Cyrille-de-Brebisson/eq_control/Firmware/eqControl_Ino/catalogs.h

// This code is copyright Cyrille de Brebisson
// Contact me if you want to use all or part of it.
// Most likely I will say yes unless it is for commercial use at which point we can discuss

void getRaDecPos(uint8_t const *s, int32_t &ra, int32_t &dec) // extract ra/dec from 3 program memory bytes that containthe data with 12 bit precision
{
    uint8_t b1= pgm_read_byte(s), b2= pgm_read_byte(s+1), b3= pgm_read_byte(s+2);
    ra= (b1+(uint32_t(b2&0xf)<<8))*(24*3600L)/4096;
    dec= ((b2>>4)+(uint32_t(b3)<<4))*(180*3600L)/4096-90*3600L;
}

// NCG Objects with Mag up to 11,  738 items: 2.9Kb bytes
// iDiff is the difference in index from NgcDiff[i+1] to NgcDiff[i]. Saves 700 bytes compared with using a 16 bit number...
// so first object is ngc40, followed by ngc45 and 55
struct { uint8_t idDiff; uint8_t radec[3]; } const NgcDiff[] PROGMEM ={
    { 40, {37, 32, 231}},
    { 5, {40, 0, 95}},
    { 10, {42, 64, 72}},
    { 48, {72, 64, 215}},
    { 1, {68, 112, 25}},
    { 17, {76, 64, 26}},
    { 8, {84, 160, 213}},
    { 4, {88, 16, 218}},
    { 1, {86, 176, 80}},
    { 12, {94, 0, 218}},
    { 1, {94, 240, 196}},
    { 10, {98, 0, 116}},
    { 28, {111, 176, 196}},
    { 3, {125, 80, 249}},
    { 1, {112, 208, 214}},
    { 16, {114, 64, 187}},
    { 5, {115, 64, 108}},
    { 11, {121, 16, 186}},
    { 3, {121, 176, 186}},
    { 1, {123, 208, 215}},
    { 21, {133, 16, 111}},
    { 1, {133, 112, 98}},
    { 6, {135, 0, 92}},
    { 25, {148, 160, 195}},
    { 3, {150, 128, 208}},
    { 7, {150, 48, 90}},
    { 12, {156, 96, 74}},
    { 30, {160, 224, 24}},
    { 16, {168, 80, 25}},
    { 16, {179, 48, 27}},
    { 19, {194, 144, 215}},
    { 23, {197, 192, 178}},
    { 15, {194, 80, 24}},
    { 17, {215, 160, 211}},
    { 21, {224, 240, 210}},
    { 31, {232, 112, 135}},
    { 36, {241, 128, 141}},
    { 35, {254, 0, 218}},
    { 19, {1, 193, 95}},
    { 3, {9, 81, 214}},
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
};

static int const nbNgc= sizeof(NgcDiff)/sizeof(NgcDiff[0])-12; // the last 12 objects are not NGC, but messiers or cadwell that are not ngcs...

class CNgc { public: // A class for scanning through ngs... works incrementally due to the idiff...
    uint16_t internalId= 0; // indicate internal id (0 to nbNgc-1)
    uint16_t externalId= 40; // indicate NGC number of current NGC
    void next() { if (internalId>=nbNgc-1) return; internalId++; externalId+= pgm_read_byte(&(NgcDiff[internalId].idDiff)); }
    void prev() { if (internalId==0) return; externalId-= pgm_read_byte(&(NgcDiff[internalId].idDiff)); internalId--; }
    void pos(int32_t &ra, int32_t &dec) { getRaDecPos(NgcDiff[internalId].radec, ra, dec); }
} Ngc;

// Messiers and Cadwell are pointers to ngc numbers. These are 10 bit packed to save around 300 bytes
static uint8_t const MessierToNgc10[] PROGMEM = {152, 64, 27, 31, 136, 17, 106, 41, 230, 154, 73, 238, 72, 169, 140, 46, 102, 217, 236, 159, 129, 2, 250, 227, 153, 110, 54, 58, 38, 159, 248, 74, 250, 42, 161, 184, 74, 43, 65, 4, 42, 16, 113, 139, 38, 172, 80, 18, 109, 190, 208, 132, 66, 202, 67, 94, 200, 243, 206, 65, 168, 89, 179, 158, 187, 225, 93, 90, 106, 168, 153, 242, 38, 156, 113, 144, 245, 72, 222, 117, 96, 137, 117, 81, 111, 134, 62, 234, 170, 175, 192, 178, 0, 171, 11, 72, 168, 34, 137, 135, 43, 181, 212, 30, 102, 153, 113, 182, 154, 107, 182, 233, 86, 155, 146, 245, 68, 135, 148, 82, 90, 13, 166, 152, 100, 249, 229, 119, 130, 111, 77, 45, 134, 162, 85, 116, 61, 0, };
uint16_t const nbMessier= 110;
static uint8_t const CadwellToNgc10[] PROGMEM = {13, 0, 128, 88, 177, 250, 202, 169, 78, 9, 251, 202, 192, 46, 175, 34, 232, 176, 42, 183, 10, 48, 192, 175, 176, 163, 189, 203, 195, 19, 236, 36, 102, 171, 13, 223, 137, 219, 239, 112, 191, 246, 186, 221, 109, 181, 226, 118, 78, 88, 254, 14, 123, 175, 185, 239, 41, 147, 171, 70, 195, 20, 243, 111, 115, 51, 253, 67, 44, 5, 169, 130, 243, 211, 93, 120, 85, 240, 109, 56, 22, 20, 168, 196, 166, 68, 106, 160, 143, 0, 140, 208, 20, 98, 141, 230, 197, 201, 19, 122, 76, 174, 200, 221, 124, 0, 91, 233, 196, 130, 29, 134, 84, 213, 82, 158, 82, 167, 97, 64, 106, 1, 23, 176, 192, 157, 14, 188, 74, 7, 216, 17, 240, 225, 101, 58, 1, };
uint16_t const nbCadwell= 109;
static uint16_t read10bits(uint8_t const *p, uint8_t v) // read the nth 10 bit number from lists above...
{
    uint16_t t= pgm_read_word(p+((v*10)>>3)); 
    t= (t>>((v&3)*2))&1023;
    return t;
}

// named star catalog. 1507 bytes, (133 stars)
// form is 3 bytes ra/dec on a 0-4095 range 
// then 1 byte: star name size -3 (low order nibble) and previous's start name size-3 (high order nibble) (for backward scann)
// and finally the star name
// Note that should we move the star name to 5 bit per character, we could save around 300 bytes!
class CStars { public:
    // This class handles the star list, giving you a pointer on a star and allowing you to go througth it as you want and get the info...
    uint8_t const *s= stars;      // pointer to current selected star
    static const int nb= 133;     // total number of stars
    uint8_t id= 0;                // id of current star (to avoid going past ends)
    static uint8_t const stars[]; // star table...
    void next() { if (id>=nb-1) return; id++; s= s+4+(pgm_read_byte(s+3)&15)+3; }
    void prev() { if (id==0) return; id--; s= s-4-(((pgm_read_byte(s+3)>>4)&15)+3); }
    void pos(int32_t &ra, int32_t &dec) { getRaDecPos(s, ra, dec); }
    int8_t name(char *n) { int8_t l= (pgm_read_byte(s+3)&15)+3; int8_t l2= l; n[l]= 0; while (--l>=0) n[l]=pgm_read_byte(s+4+l); return l2; } // copy current star name in n. return it's size. max=18
} stars;
uint8_t const CStars::stars[] PROGMEM ={
    251, 161, 70,  0x03,'A','c','a','m','a','r', //Acamar
    21, 145, 46,  0x35,'A','c','h','e','r','n','a','r', //Achernar
    75, 72, 38,  0x52,'A','c','r','u','x', //Acrux
    166, 196, 86,  0x23,'A','d','h','a','r','a', //Adhara
    198, 28, 98,  0x35,'A','l','b','a','l','d','a','h', //Albaldah
    2, 205, 167,  0x54,'A','l','b','i','r','e','o', //Albireo
    242, 56, 206,  0x42,'A','l','c','o','r', //Alcor
    135, 66, 162,  0x24,'A','l','c','y','o','n','e', //Alcyone
    16, 115, 151,  0x46,'A','l','d','e','b','a','r','a','n', //Aldebaran
    52, 14, 217,  0x66,'A','l','d','e','r','a','m','i','n', //Alderamin
    37, 144, 149,  0x64,'A','l','g','e','n','i','b', //Algenib
    227, 54, 156,  0x44,'A','l','g','i','e','b','a', //Algieba
    23, 50, 186,  0x42,'A','l','g','o','l', //Algol
    84, 136, 104,  0x24,'A','l','g','o','r','a','b', //Algorab
    107, 84, 151,  0x43,'A','l','h','e','n','a', //Alhena
    153, 152, 207,  0x33,'A','l','i','o','t','h', //Alioth
    49, 41, 198,  0x33,'A','l','k','a','i','d', //Alkaid
    96, 49, 188,  0x33,'A','l','m','a','a','k', //Almaak
    194, 62, 61,  0x33,'A','l','n','a','i','r', //Alnair
    160, 163, 168,  0x33,'A','l','n','a','t','h', //Alnath
    188, 67, 126,  0x34,'A','l','n','i','l','a','m', //Alnilam
    201, 51, 125,  0x44,'A','l','n','i','t','a','k', //Alnitak
    78, 166, 115,  0x44,'A','l','p','h','a','r','d', //Alphard
    98, 250, 165,  0x45,'A','l','p','h','e','k','k','a', //Alphekka
    23, 80, 169,  0x56,'A','l','p','h','e','r','a','t','z', //Alpheratz
    71, 29, 137,  0x64,'A','l','s','h','a','i','n', //Alshain
    59, 157, 140,  0x43,'A','l','t','a','i','r', //Altair
    239, 84, 86,  0x33,'A','l','u','d','r','a', //Aludra
    74, 208, 67,  0x32,'A','n','k','a','a', //Ankaa
    254, 106, 90,  0x24,'A','n','t','a','r','e','s', //Antares
    129, 73, 155,  0x45,'A','r','c','t','u','r','u','s', //Arcturus
    178, 163, 102,  0x52,'A','r','n','e','b', //Arneb
    53, 219, 29,  0x22,'A','t','r','i','a', //Atria
    149, 85, 43,  0x22,'A','v','i','o','r', //Avior
    40, 15, 207,  0x2b,'B','a','b','c','o','c','k','\'','s',' ','s','t','a','r', //Babcock's star
    249, 171, 134,  0xbb,'B','a','r','n','a','r','d','\'','s',' ','S','t','a','r', //Barnard's Star
    135, 24, 43,  0xb3,'B','e','c','r','u','x', //Becrux
    156, 3, 137,  0x36,'B','e','l','l','a','t','r','i','x', //Bellatrix
    242, 131, 138,  0x67,'B','e','t','e','l','g','e','u','s','e', //Betelgeuse
    68, 4, 53,  0x74,'C','a','n','o','p','u','s', //Canopus
    132, 99, 193,  0x44,'C','a','p','e','l','l','a', //Capella
    26, 16, 212,  0x41,'C','a','p','h', //Caph
    13, 85, 173,  0x13,'C','a','s','t','o','r', //Castor
    208, 123, 134,  0x35,'C','e','b','a','l','r','a','i', //Cebalrai
    161, 80, 214,  0x50,'C','i','h', //Cih
    159, 120, 182,  0x07,'C','o','r',' ','C','a','r','o','l','i', //Cor Caroli
    107, 195, 120,  0x72,'C','u','r','s','a', //Cursa
    80, 29, 178,  0x27,'C','y','g','n','u','s',' ','X','-','1', //Cygnus X-1
    203, 109, 192,  0x72,'D','e','n','e','b', //Deneb
    224, 183, 148,  0x25,'D','e','n','e','b','o','l','a', //Denebola
    123, 96, 102,  0x53,'D','i','p','h','d','a', //Diphda
    171, 218, 95,  0x35,'D','s','c','h','u','b','b','a', //Dschubba
    95, 215, 215,  0x52,'D','u','b','h','e', //Dubhe
    125, 14, 142,  0x21,'E','n','i','f', //Enif
    246, 59, 201,  0x13,'E','t','a','m','i','n', //Etamin
    78, 223, 85,  0x36,'F','o','m','a','l','h','a','u','t', //Fomalhaut
    88, 200, 46,  0x63,'G','a','c','r','u','x', //Gacrux
    216, 93, 176,  0x33,'G','i','e','n','a','h', //Gienah
    44, 8, 103,  0x3a,'G','i','e','n','a','h',' ','G','h','u','r','a','b', //Gienah Ghurab
    247, 196, 139,  0xa4,'G','o','m','e','i','s','a', //Gomeisa
    186, 218, 99,  0x45,'G','r','a','f','f','i','a','s', //Graffias
    235, 167, 181,  0x5d,'G','r','o','o','m','b','r','i','d','g','e',' ','1','8','3','0', //Groombridge 1830
    96, 41, 42,  0xd2,'H','a','d','a','r', //Hadar
    105, 81, 161,  0x22,'H','a','m','a','l', //Hamal
    76, 35, 175,  0x25,'H','a','s','s','a','l','e','h', //Hassaleh
    186, 147, 119,  0x53,'H','a','t','s','y','a', //Hatsya
    213, 137, 166,  0x31,'I','z','a','r', //Izar
    118, 243, 63,  0x1b,'K','a','p','t','e','y','n','\'','s',' ','S','t','a','r', //Kapteyn's Star
    68, 28, 79,  0xbb,'K','a','u','s',' ','A','u','s','t','r','a','l','i','s', //Kaus Australis
    79, 220, 91,  0xba,'K','a','u','s',' ','B','o','r','e','a','l','i','s', //Kaus Borealis
    59, 156, 85,  0xae,'K','a','u','s',' ','M','e','r','i','d','i','o','n','a','l','i','s', //Kaus Meridionalis
    229, 121, 233,  0xe3,'K','o','c','h','a','b', //Kochab
    0, 155, 158,  0x38,'K','o','r','n','e','p','h','o','r','o','s', //Kornephoros
    97, 184, 94,  0x81,'K','r','a','z', //Kraz
    98, 159, 149,  0x13,'M','a','r','k','a','b', //Markab
    36, 255, 170,  0x32,'M','a','t','a','r', //Matar
    43, 24, 209,  0x23,'M','e','g','r','e','z', //Megrez
    254, 227, 191,  0x37,'M','e','n','k','a','l','i','n','a','n', //Menkalinan
    6, 210, 133,  0x73,'M','e','n','k','a','r', //Menkar
    104, 73, 76,  0x34,'M','e','n','k','e','n','t', //Menkent
    90, 55, 208,  0x42,'M','e','r','a','k', //Merak
    37, 214, 28,  0x28,'M','i','a','p','l','a','c','i','d','u','s', //Miaplacidus
    176, 147, 127,  0x84,'M','i','n','t','a','k','a', //Mintaka
    140, 193, 123,  0x41,'M','i','r','a', //Mira
    198, 160, 178,  0x13,'M','i','r','a','c','h', //Mirach
    69, 226, 198,  0x34,'M','i','r','p','h','a','k', //Mirphak
    64, 116, 102,  0x43,'M','i','r','z','a','m', //Mirzam
    238, 24, 206,  0x32,'M','i','z','a','r', //Mizar
    70, 41, 154,  0x23,'M','u','f','r','i','d', //Mufrid
    95, 21, 71,  0x31,'N','a','o','s', //Naos
    16, 188, 84,  0x11,'N','a','s','h', //Nash
    165, 115, 98,  0x12,'N','i','h','a','l', //Nihal
    157, 156, 90,  0x22,'N','u','n','k','i', //Nunki
    27, 17, 48,  0x26,'p',' ','E','r','i','d','a','n','i', //p Eridani
    158, 77, 47,  0x64,'P','e','a','c','o','c','k', //Peacock
    238, 87, 204,  0x41,'P','h','a','d', //Phad
    198, 131, 79,  0x12,'P','h','a','k','t', //Phakt
    175, 241, 254,  0x24,'P','o','l','a','r','i','s', //Polaris
    43, 213, 167,  0x43,'P','o','l','l','u','x', //Pollux
    118, 248, 125,  0x34,'P','o','r','r','i','m','a', //Porrima
    26, 101, 135,  0x44,'P','r','o','c','y','o','n', //Procyon
    130, 198, 161,  0x4e,'R','a','s',' ','E','l','.',' ','A','u','s','t','r','a','l','i','s', //Ras El. Australis
    126, 123, 148,  0xe7,'R','a','s','a','l','g','e','t','h','i', //Rasalgethi
    184, 219, 145,  0x77,'R','a','s','a','l','h','a','g','u','e', //Rasalhague
    171, 107, 202,  0x75,'R','a','s','t','a','b','a','n', //Rastaban
    56, 212, 112,  0x5a,'R','e','d',' ','R','e','c','t','a','n','g','l','e', //Red Rectangle
    194, 6, 145,  0xa4,'R','e','g','u','l','u','s', //Regulus
    126, 83, 116,  0x42,'R','i','g','e','l', //Rigel
    198, 121, 41,  0x2c,'R','i','g','i','l',' ','K','e','n','t','a','u','r','u','s', //Rigil Kentaurus
    244, 160, 213,  0xc4,'R','u','c','h','b','a','h', //Ruchbah
    187, 142, 127,  0x47,'S','a','d','a','l','m','e','l','i','k', //Sadalmelik
    89, 30, 120,  0x76,'S','a','d','a','l','s','u','u','d', //Sadalsuud
    148, 77, 185,  0x61,'S','a','d','r', //Sadr
    221, 51, 114,  0x12,'S','a','i','p','h', //Saiph
    191, 219, 66,  0x23,'S','a','r','g','a','s', //Sargas
    96, 255, 167,  0x33,'S','c','h','e','a','t', //Scheat
    180, 59, 75,  0x33,'S','h','a','u','l','a', //Shaula
    115, 96, 208,  0x33,'S','h','e','d','i','r', //Shedir
    142, 124, 175,  0x34,'S','h','e','l','i','a','k', //Sheliak
    70, 145, 157,  0x45,'S','h','e','r','a','t','a','n', //Sheratan
    128, 52, 104,  0x53,'S','i','r','i','u','s', //Sirius
    242, 40, 112,  0x32,'S','p','i','c','a', //Spica
    46, 29, 143,  0x24,'T','a','r','a','z','e','d', //Tarazed
    97, 137, 219,  0x43,'T','h','u','b','a','n', //Thuban
    48, 182, 43,  0x33,'T','u','r','e','i','s', //Tureis
    125, 42, 137,  0x36,'U','n','u','k','a','l','h','a','i', //Unukalhai
    105, 44, 183,  0x61,'V','e','g','a', //Vega
    176, 152, 143,  0x19,'V','i','n','d','e','m','i','a','t','r','i','x', //Vindemiatrix
    194, 116, 90,  0x92,'W','e','z','e','n', //Wezen
    165, 194, 108,  0x23,'Z','a','u','r','a','k', //Zaurak
    125, 55, 157,  0x32,'Z','o','s','m','a', //Zosma
    230, 41, 105,  0x2a,'Z','u','b','e','n','e','l','g','e','n','u','b','i', //Zubenelgenubi
    48, 170, 114,  0xab,'Z','u','b','e','n','e','s','c','h','e','m','a','l','i', //Zubeneschemali
};
